wkcollis1-eng/DIY-LiFePO4-UPS/assets/IMG_1909.jpeg

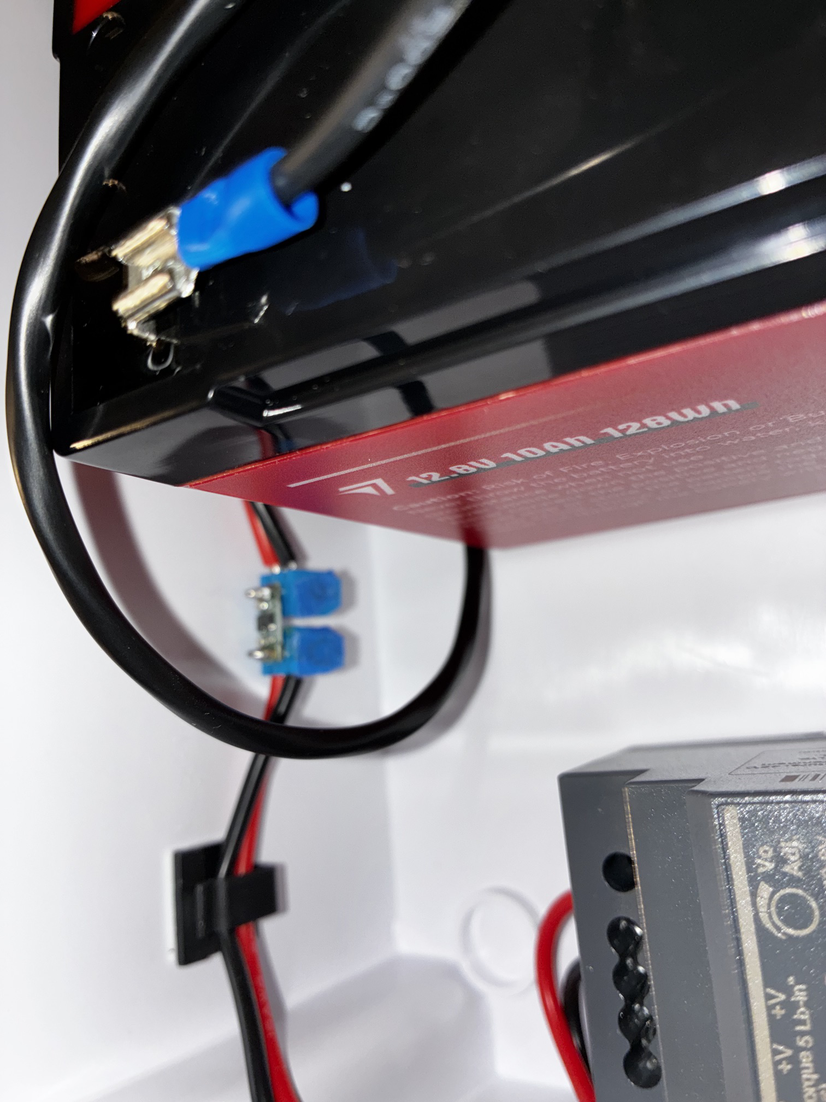
assets/IMG_1909.jpeg
