wkcollis1-eng/DIY-LiFePO4-UPS/assets/IMG_1910.jpeg

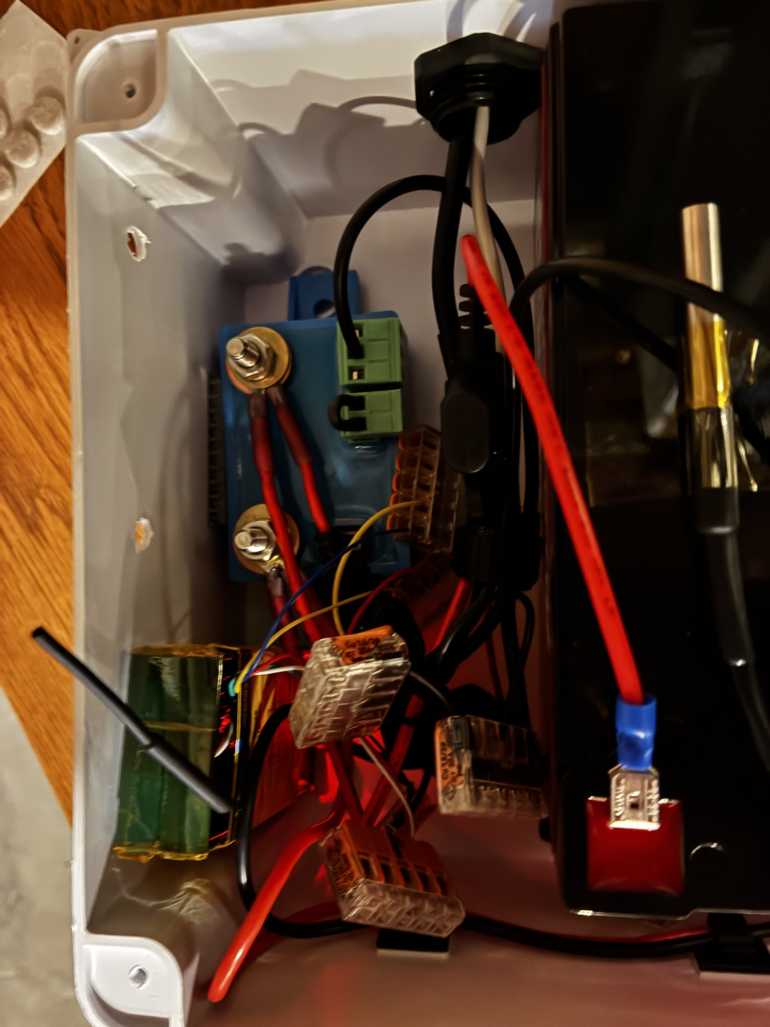
assets/IMG_1910.jpeg
