wkcollis1-eng/DIY-LiFePO4-UPS/assets/IMG_1911.jpeg

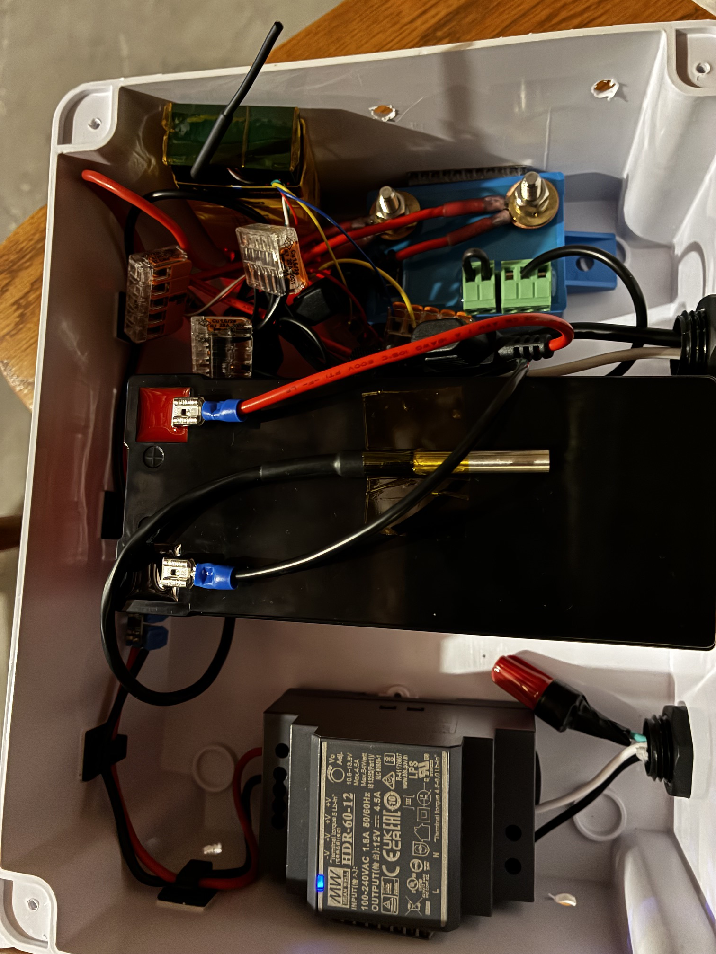
assets/IMG_1911.jpeg
