wkcollis1-eng/DIY-LiFePO4-UPS/UPS-Monitor/UPS-Monitor-THT.png

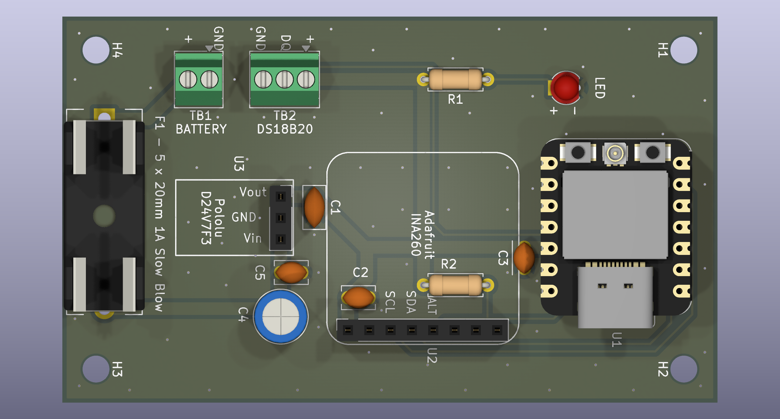
UPS-Monitor/UPS-Monitor-THT.png
