wkcollis1-eng/DIY-LiFePO4-UPS/UPS-Monitor/UPS-Monitor-THT_View 5.png

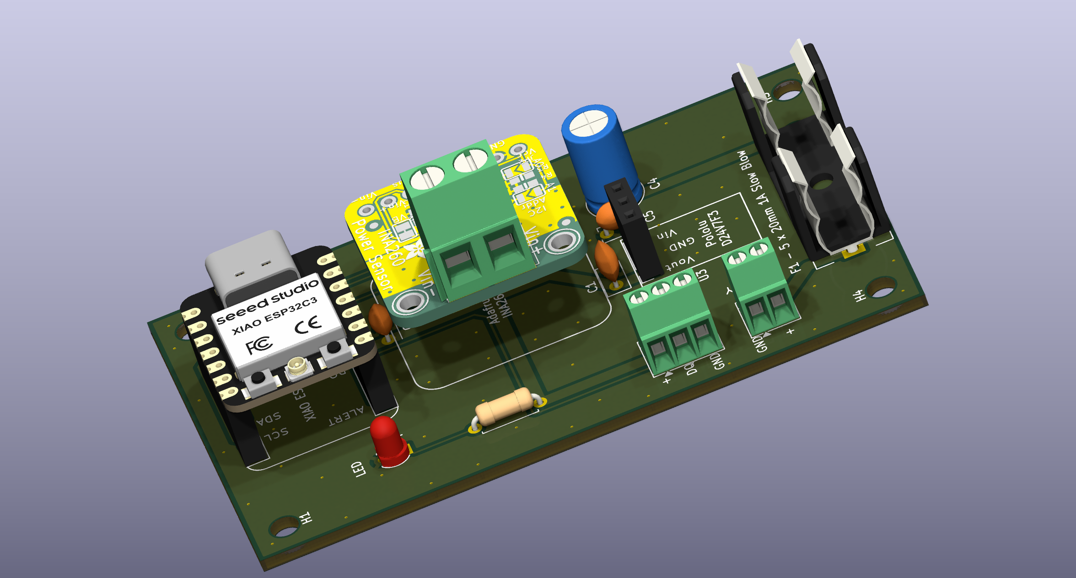
UPS-Monitor/UPS-Monitor-THT_View 5.png
