wkcollis1-eng/DIY-LiFePO4-UPS/UPS-Monitor/UPS-Monitor-THT_View Top.png

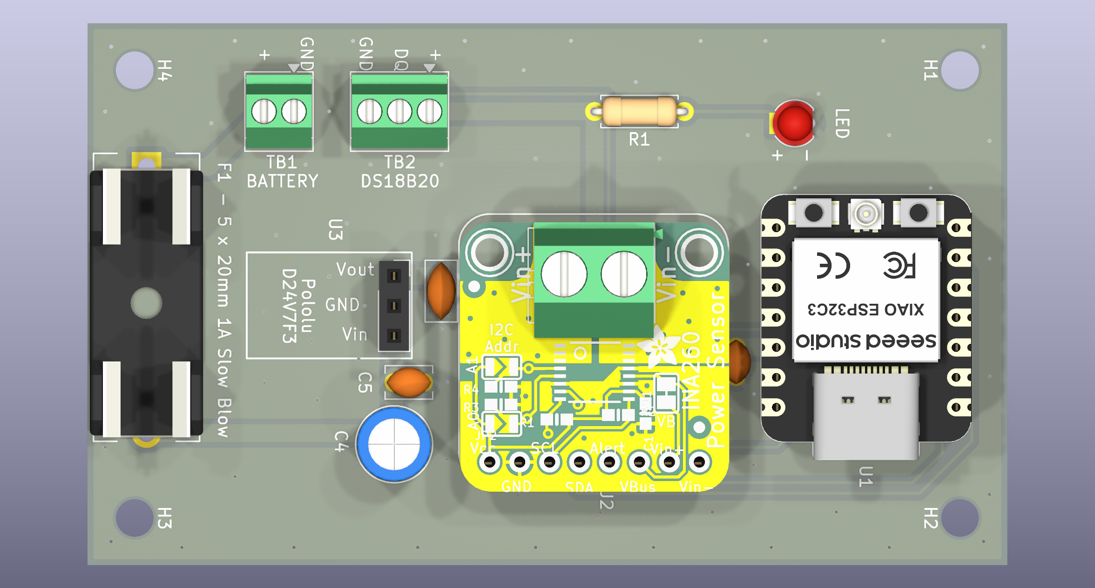
UPS-Monitor/UPS-Monitor-THT_View Top.png
