wkcollis1-eng/DIY-LiFePO4-UPS/docs/commissioning.md

# Commissioning Test Report

**System:** DIY LiFePO4 UPS for Home Assistant Green & Xfinity XB7 Modem
**Date:** March 25–27, 2026
**Location:** East Hampton, CT — basement, 53°F (11.7°C)
**Status:** Commissioned ✅

---

## Overview

This document records the commissioning tests performed following initial build completion. Tests were conducted in sequence: power baseline characterization, initial functional verification, full discharge cycle validation with a substitute load, and final validation with the design load. All results are compared against the system specifications in [docs/specifications.md](specifications.md).

---

## 1. Pre-Commission Power Baseline

### 1.1 XB7 Standalone Measurement

Before UPS assembly, the Xfinity XB7 modem was placed on a Kill-a-Watt meter running on its OEM AC adapter to establish the standalone DC load baseline.

| Parameter | Value |
|---|---|
| Measurement duration | 72.4 hours |
| Energy consumed | 1.066 kWh |
| Average AC wall draw | **14.7W** |
| Adapter model | NBC56B120460VU (DoE Level VI, ≥88% efficiency) |
| Derived DC load | ~12.9W (at 88% adapter efficiency) |
| Peak AC wall draw | 20.3W |

### 1.2 Combined Bare-Wall Baseline (XB7 + HA Green)

Both devices were measured together through OEM AC adapters over an extended multi-window measurement.

| Measurement Window | Duration | Energy | Average |
|---|---|---|---|
| Window 1 | 118.25 hr | — | 16.0W |
| Window 2 | 135.0 hr | — | 16.0W |
| Window 3 | 158.8 hr | 2.538 kWh | **16.0W** |
| Window 4 (8d 1h 46m) | 193.8 hr | 3.103 kWh | **16.02W** |
| Window 5 (21d 21h 5m) | 525.1 hr | 8.274 kWh | **15.76W** |

**Result:** 16.0W average confirmed stable across five successive measurement windows spanning 21+ days. Peak 23W confirmed in three independent windows. Baseline is definitively established.

> **Note:** The vacation period (windows 4–5) validated that XB7 draw is load-independent — the modem maintains DOCSIS channel lock and timing synchronization regardless of traffic, and the HA Green contribution (~1.3W, ~8% of total) is not meaningfully affected by reduced automation activity.

---

## 2. Initial Functional Verification

### 2.1 Ideal Diode Backfeed Test

With AC disconnected and the battery powering the R6400 router load, PSU output terminal voltage was measured with a DMM.

| Parameter | Expected | Measured |
|---|---|---|
| PSU terminal voltage (AC off) | ~0V (blocked) | **0.10V** |

**Result:** 0.10V at PSU terminals confirms the ideal diode is blocking correctly. True 0V is not achievable with a real MOSFET — the measured voltage is the result of microamp-level leakage current through the discharged PSU output impedance. This is the expected behavior and not harmful to the PSU.

### 2.2 Battery Current Measurement

DC current was measured at the battery positive terminal with the PSU disconnected and the R6400 router as the sole load.

| Parameter | Value |
|---|---|
| Measured current | **0.54A** |
| Derived DC load | ~7W (0.54A × 13V) |
| Expected at design load | ~1.2A (~14.5W) |

**Result:** 0.54A is consistent with the R6400 router load. Confirms current path through BP-65 is intact and load current is within expected range for this substitute load.

### 2.3 Voltage Drop Validation

Pre-disconnect float voltage measured by Shelly Plus Uni ADC averaged **13.24–13.26V** at the battery terminals with the PSU at 13.3V setpoint.

Per the voltage drop analysis (Path 2, PSU → Battery at 1.2A typical):

| Parameter | Calculated | Measured | Delta |
|---|---|---|---|
| Path resistance | 50.1 mΩ | — | — |
| Voltage drop at 1.2A | 0.060V | ~0.06V | <0.01V |
| Battery terminal voltage | 13.24V | **13.24–13.26V** | ✅ |

**Result:** Measured float voltage matches the calculated value to within ADC resolution. Voltage drop analysis validated.

---

## 3. Discharge Cycle Test — Substitute Load (R6400 Router)

### 3.1 Test Configuration

The R6400 router was used as a substitute load (~7W DC, ~0.54A) in place of the design load (XB7 + HA Green, ~14.5W DC, ~1.2A). Two complete discharge cycles were performed over a 27-hour period with battery voltage logged via the Shelly Plus Uni at 5-second intervals.

### 3.2 Discharge 1

| Parameter | Value |
|---|---|
| Start time | 17:19 UTC, March 25, 2026 |
| Start voltage | 13.19V |
| End voltage | 12.98V |
| Duration | **7.76 hours** |
| Voltage drop | 0.21V |
| AC restored | 01:05 UTC, March 26, 2026 |

The LiFePO4 discharge plateau was clearly visible — voltage dropped only 0.21V over 7.76 hours at the reduced load. The battery was not meaningfully discharged; the plateau extends to approximately 20% SoC before the knee appears.

### 3.3 Recharge

AC was restored and the PSU resumed 13.3V output.

| Parameter | Value |
|---|---|
| Duration | 10.1 hours |
| Peak recharge voltage | 13.28V |
| Float plateau | 13.24–13.27V |
| Start voltage for Discharge 2 | 13.04V (partial recharge) |

The recharge voltage held stable at 13.24–13.27V through the float period, consistent with the bulk charge phase tapering toward equilibrium. The battery was not at full charge when Discharge 2 began, as indicated by the 13.04V starting voltage.

### 3.4 Discharge 2 — LVD Validation

| Parameter | Value |
|---|---|
| Start time | 11:13 UTC, March 26, 2026 |
| Start voltage | 13.04V (partial charge) |
| Duration | **9.36 hours** |
| Minimum voltage reached | 11.77V |
| BP-65 LVD trip | ✅ Confirmed |
| AC restored | ~20:36 UTC, March 26, 2026 |

The discharge curve was textbook LiFePO4 — a long flat plateau from 13.04V to approximately 12.60V over ~8.5 hours, followed by a rapid knee descent to 11.77V. The Victron BP-65 disconnected loads at this point (90-second hold-off timer elapsed), protecting the battery from further discharge.

**Key observation — OCV recovery test:** During Discharge 2 at approximately t+5.3h (12.88V), the router was briefly unplugged and reconnected. Voltage spiked from 12.88V to 13.02V (+0.14V) then returned to the load-under curve.

This 0.14V OCV recovery at 0.54A load implies:

**R_internal = 0.14V ÷ 0.54A ≈ 260 mΩ**

This is elevated relative to the wiring path resistance (47 mΩ) and confirms that battery internal resistance dominates at low SoC near the discharge knee — expected behavior for LiFePO4 in this region of the discharge curve.

### 3.5 Discharge Cycle Summary

| Parameter | Spec | Discharge 1 | Discharge 2 |
|---|---|---|---|
| LFP plateau flatness | Very flat | 0.21V / 7.76h ✅ | Extended plateau ✅ |
| LVD trip voltage | 11.80V | Not reached | **11.77V** ✅ |
| BP-65 LVD function | Confirmed | — | **Confirmed** ✅ |
| Post-restore recovery | <1h to float | ✅ | ✅ |

> **Runtime note:** Discharge 2 ran 9.36 hours from 13.04V (partial charge) at ~7W DC. The design load of 14.5W DC from full charge (13.20V) projects to the specified 7.8 hours, consistent with this result.

---

## 4. Post-Discharge Float Characterization

Following AC restoration after Discharge 2, the Shelly Plus Uni logged hourly minimum voltages from 12:00 UTC March 26 through 09:00 UTC March 27 (21 hours).

| Elapsed | Voltage | Phase |
|---|---|---|
| 0–4h | 12.87 → 12.56V | Discharge tail (logged) |
| t+4h | 11.83V | LVD trip bucket |
| t+5h onward | 13.20V | Post-restore, bulk charge |
| t+13–18h | 13.20V (stable) | Float plateau |
| t+19h | 13.24V | Current tapering |
| t+21h | 13.27V | Approaching equilibrium |

The steady rise from 13.20V → 13.27V between hours 13 and 21 reflects charging current tapering as the battery approaches PSU setpoint — consistent with the LiFePO4 post-charge relaxation behavior documented in the design. Full equilibrium at 13.28–13.30V is expected at approximately 24–28h post full-discharge.

---

## 5. Design Load Validation

### 5.1 UPS System Power Measurement

With the UPS fully assembled and powering the design load (XB7 modem + HA Green) through the HDR-60-12 PSU, a Kill-a-Watt meter measured total AC wall draw.

| Parameter | Spec (derived) | Measured | Delta |
|---|---|---|---|
| Duration | — | 5h 6m | — |
| Energy consumed | — | 0.092 kWh | — |
| Average AC wall draw | ~17.9W | **18.04W** | +0.14W (+0.8%) |
| Derived DC load | 14.5W | **14.61W** (at 81% PSU eff.) | +0.11W |
| Peak AC wall draw | ~24.9W (derived) | **27.3W** | +2.4W |
| Annual AC energy | 157 kWh | **158.0 kWh** | — |
| Annual operating cost | ~$46/yr | **~$45.8/yr** | — |

**Result:** Average draw matches spec within 0.8%. The 7.8h runtime estimate is unaffected. Annual cost estimate is confirmed.

**Peak power note:** The 27.3W measured peak exceeds the derived estimate of ~24.9W by 2.4W. This reflects PSU efficiency degradation during transient loading — the HDR-60-12 efficiency at peak load is lower than the 81% typical figure used in the derivation. The spec table peak figure should be updated from the derived value to the measured 27.3W AC / ~22.1W DC.

### 5.2 UPS Operating Cost vs Alternatives

| Option | Avg Draw | Annual kWh | Annual Cost |
|---|---|---|---|
| Bare wall warts (no UPS) | 16.0W measured | 140 kWh | ~$40.6/yr |
| This DIY UPS (measured) | 18.04W | 158 kWh | **~$45.8/yr** |
| APC BE600M1 (estimated) | ~20W | 175 kWh | ~$50.8/yr |

UPS overhead vs bare wall warts: **+2.04W, +$5.2/yr** — the UPS capability costs approximately $5/year to operate, consistent with the design target.

---

## 6. Commissioning Status

| Test | Result | Notes |
|---|---|---|
| Ideal diode backfeed blocking | ✅ Pass | 0.10V at PSU terminals (leakage only) |
| Voltage drop at float | ✅ Pass | 13.24–13.26V measured vs 13.24V calculated |
| LiFePO4 discharge plateau | ✅ Pass | Textbook flat curve confirmed |
| BP-65 LVD disconnect | ✅ Pass | Tripped at 11.77–11.80V |
| BP-65 LVD reconnect | ✅ Pass | PSU restored loads immediately on AC return |
| Post-restore recharge | ✅ Pass | Float re-established within 1h |
| Design load power (avg) | ✅ Pass | 18.04W vs 17.9W spec (+0.8%) |
| Design load power (peak) | ⚠️ Note | 27.3W measured vs ~24.9W derived — update spec |
| Runtime projection | ✅ Consistent | 7.8h estimate validated by discharge data |
| Battery temperature (commissioning) | ✅ Pass | 52.6–59.6°F (11.4–15.3°C) — 24°C below 40°C alert threshold |
| Annual operating cost | ✅ Pass | $45.8/yr vs $46/yr spec |
| HA Green graceful shutdown | ⬜ Pending | Requires design load outage test |
| Shelly 12.2V shutdown trigger | ⬜ Pending | Requires design load outage test |

---

## 7. Open Items

1. **HA Green graceful shutdown** — a full discharge test with the design load (XB7 + HA Green) running is required to validate that the Shelly Plus Uni triggers HA Green shutdown at 12.2V with 15–20 minutes of runtime remaining before LVD. The R6400 substitute load test could not validate this automation path.

2. **Peak power spec update** — update `specifications.md` peak AC wall draw from ~24.9W (derived) to **27.3W** (measured).

3. **HA automation documentation** — Shelly Plus Uni HA integration YAML to be published in `docs/` once validated with design load outage test.

---

## Appendix A — Temperature Observations

The DS18B20 sensor was mounted against the battery case midpoint per the assembly procedure. Commissioning took place in the basement at 53°F (11.7°C). Measured temperatures throughout the 27-hour test ranged from **52.6°F to 59.6°F (11.4°C to 15.3°C)**, with a mean of 55.0°F (12.8°C).

> **Note:** Temperature data was logged by the Shelly Plus Uni in °F. All values below are in both °F and °C for clarity.

| Parameter | °F | °C |
|---|---|---|
| Ambient (basement) | 53°F | 11.7°C |
| Battery minimum | 52.6°F | 11.4°C |
| Battery maximum | 59.6°F | 15.3°C |
| Battery mean | 55.0°F | 12.8°C |
| HA warning threshold | 104°F | **40°C** |
| Headroom below threshold | >44°F | >24°C |

**Result: Thermal management confirmed adequate.** The DS18B20 is reading battery surface temperature directly, buffered below ambient by the battery's thermal mass. The 40°C HA warning threshold has more than 24°C of headroom above the measured operating range.

**Implications for battery longevity:** LiFePO4 calendar aging is strongly temperature-dependent. The design specification's 10–20 year lifespan estimate was based on moderate temperature operation (63–75°F / 17–24°C). At the measured operating range of 11–15°C, calendar aging proceeds more slowly — the lifespan projection is likely conservative for basement installation. Once relocated to the intended second-floor climate-controlled installation environment (63–75°F / 17–24°C), temperatures will rise but remain well within the design envelope and safely below the 40°C alert threshold.

> No thermal concern exists at either the commissioning location or the intended installation environment. Thermal runaway threshold for LiFePO4 is >270°C — operating temperatures are a negligible fraction of that limit.
