wkcollis1-eng/DIY-LiFePO4-UPS/data/Test_D3_March_2026_Voltage.csv

entity_id | state | last_changed
sensor.ups_battery_voltge_ups_battery_voltage_voltmeter | 13.27 | 2026-03-26T10:00:00.000Z
sensor.ups_battery_voltge_ups_battery_voltage_voltmeter | 13.26 | 2026-03-26T10:00:00.464Z
sensor.ups_battery_voltge_ups_battery_voltage_voltmeter | 13.27 | 2026-03-26T10:00:02.460Z
sensor.ups_battery_voltge_ups_battery_voltage_voltmeter | 13.26 | 2026-03-26T10:01:00.370Z
sensor.ups_battery_voltge_ups_battery_voltage_voltmeter | 13.27 | 2026-03-26T10:01:02.361Z
sensor.ups_battery_voltge_ups_battery_voltage_voltmeter | 13.25 | 2026-03-26T10:01:37.308Z
sensor.ups_battery_voltge_ups_battery_voltage_voltmeter | 13.27 | 2026-03-26T10:01:41.296Z
sensor.ups_battery_voltge_ups_battery_voltage_voltmeter | 13.26 | 2026-03-26T10:02:01.275Z
sensor.ups_battery_voltge_ups_battery_voltage_voltmeter | 13.27 | 2026-03-26T10:02:23.230Z
sensor.ups_battery_voltge_ups_battery_voltage_voltmeter | 13.26 | 2026-03-26T10:02:24.228Z
sensor.ups_battery_voltge_ups_battery_voltage_voltmeter | 13.27 | 2026-03-26T10:02:31.218Z
sensor.ups_battery_voltge_ups_battery_voltage_voltmeter | 13.26 | 2026-03-26T10:02:37.211Z
sensor.ups_battery_voltge_ups_battery_voltage_voltmeter | 13.27 | 2026-03-26T10:02:40.213Z
sensor.ups_battery_voltge_ups_battery_voltage_voltmeter | 13.26 | 2026-03-26T10:02:42.203Z
sensor.ups_battery_voltge_ups_battery_voltage_voltmeter | 13.27 | 2026-03-26T10:02:43.198Z
sensor.ups_battery_voltge_ups_battery_voltage_voltmeter | 13.26 | 2026-03-26T10:03:10.156Z
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
sensor.ups_battery_voltge_ups_battery_voltage_voltmeter | 12.97 | 2026-03-26T13:55:41.549Z
sensor.ups_battery_voltge_ups_battery_voltage_voltmeter | 12.96 | 2026-03-26T13:56:11.260Z
sensor.ups_battery_voltge_ups_battery_voltage_voltmeter | 12.97 | 2026-03-26T13:56:14.258Z
sensor.ups_battery_voltge_ups_battery_voltage_voltmeter | 12.96 | 2026-03-26T13:56:28.229Z
sensor.ups_battery_voltge_ups_battery_voltage_voltmeter | 12.97 | 2026-03-26T13:56:34.228Z
sensor.ups_battery_voltge_ups_battery_voltage_voltmeter | 12.96 | 2026-03-26T13:56:37.224Z
sensor.ups_battery_voltge_ups_battery_voltage_voltmeter | 12.94 | 2026-03-26T13:56:38.222Z
sensor.ups_battery_voltge_ups_battery_voltage_voltmeter | 12.96 | 2026-03-26T13:56:39.214Z
sensor.ups_battery_voltge_ups_battery_voltage_voltmeter | 12.97 | 2026-03-26T13:56:52.192Z
sensor.ups_battery_voltge_ups_battery_voltage_voltmeter | 12.96 | 2026-03-26T13:57:06.172Z
sensor.ups_battery_voltge_ups_battery_voltage_voltmeter | 12.97 | 2026-03-26T13:57:17.154Z
sensor.ups_battery_voltge_ups_battery_voltage_voltmeter | 12.94 | 2026-03-26T13:57:38.129Z
sensor.ups_battery_voltge_ups_battery_voltage_voltmeter | 12.96 | 2026-03-26T13:57:40.119Z
sensor.ups_battery_voltge_ups_battery_voltage_voltmeter | 12.98 | 2026-03-26T13:57:51.109Z
sensor.ups_battery_voltge_ups_battery_voltage_voltmeter | 12.96 | 2026-03-26T13:58:02.087Z
sensor.ups_battery_voltge_ups_battery_voltage_voltmeter | 12.98 | 2026-03-26T13:58:10.074Z
sensor.ups_battery_voltge_ups_battery_voltage_voltmeter | 12.96 | 2026-03-26T13:58:12.075Z
sensor.ups_battery_voltge_ups_battery_voltage_voltmeter | 12.98 | 2026-03-26T13:58:16.063Z
sensor.ups_battery_voltge_ups_battery_voltage_voltmeter | 12.97 | 2026-03-26T13:58:17.062Z
sensor.ups_battery_voltge_ups_battery_voltage_voltmeter | 12.98 | 2026-03-26T13:58:19.059Z
sensor.ups_battery_voltge_ups_battery_voltage_voltmeter | 12.97 | 2026-03-26T13:58:26.066Z
sensor.ups_battery_voltge_ups_battery_voltage_voltmeter | 12.98 | 2026-03-26T13:58:45.017Z
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
